stevey-o/bunker/3D_renderings/exterior/01_rear_iso.png

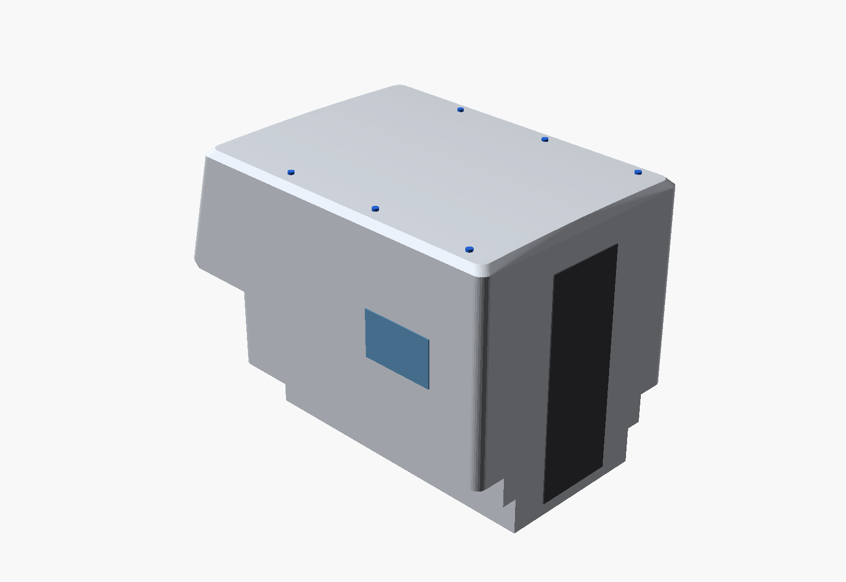
3D_renderings/exterior/01_rear_iso.png
