stevey-o/bunker/3D_renderings/exterior/05_front.png

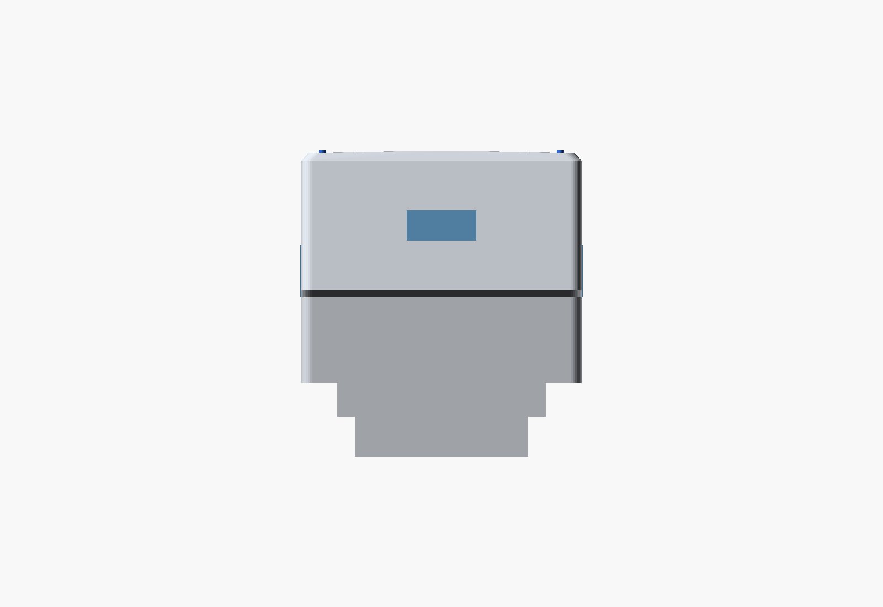
3D_renderings/exterior/05_front.png
