stevey-o/bunker/3D_renderings/exterior/07_top.png

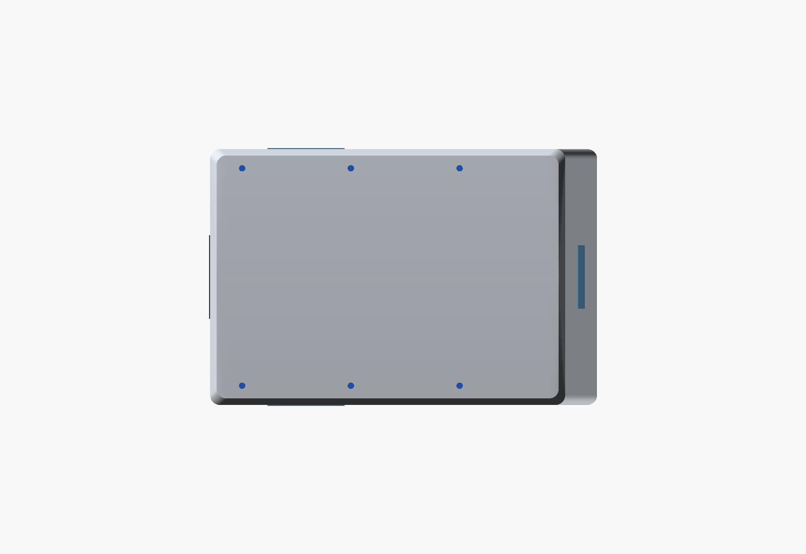
3D_renderings/exterior/07_top.png
