stevey-o/bunker/3D_renderings/fit_study/01_f150_6p5ft.png

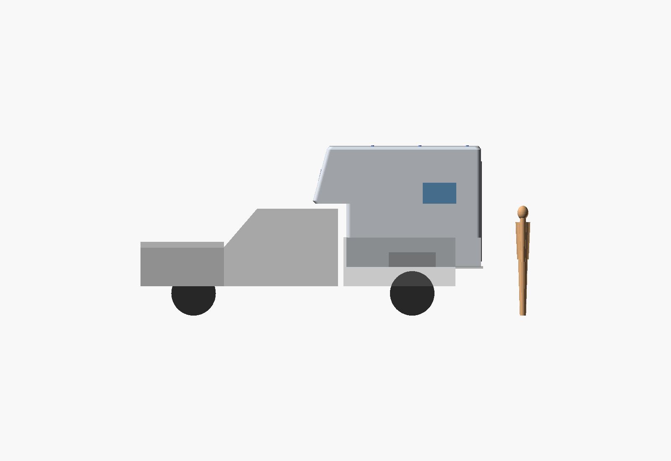
3D_renderings/fit_study/01_f150_6p5ft.png
