stevey-o/bunker/3D_renderings/fit_study/05_tacoma_rear_iso.png

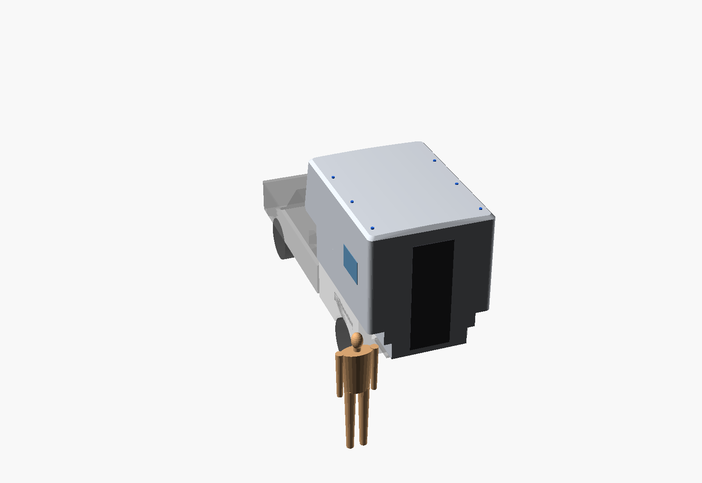
3D_renderings/fit_study/05_tacoma_rear_iso.png
