stevey-o/bunker/3D_renderings/truck_fit/01_short_bed.png

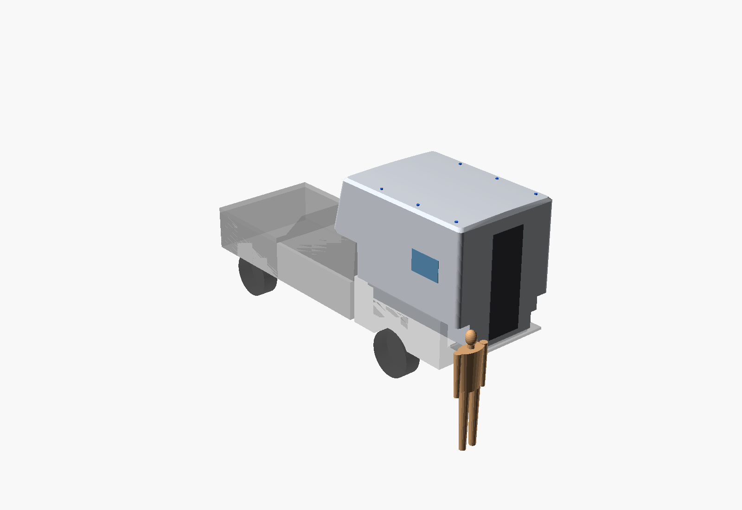
3D_renderings/truck_fit/01_short_bed.png
