stevey-o/bunker/3D_renderings/truck_fit/04_cab_clearance.png

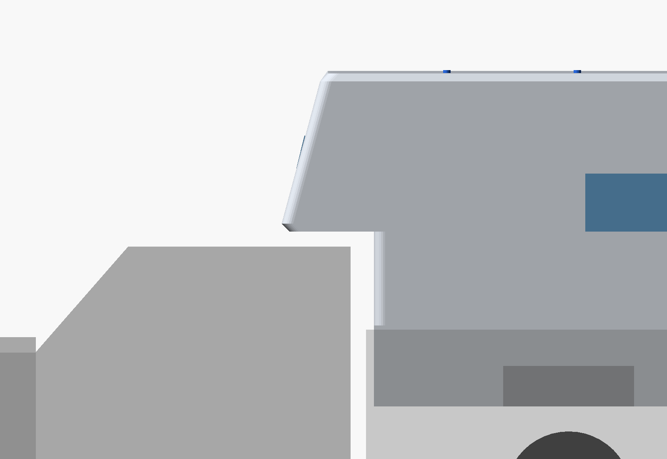
3D_renderings/truck_fit/04_cab_clearance.png
