stevey-o/bunker/cad/config/dimensions.scad

// GENERATED by scripts_code/sync_config.py from cad/config/dimensions.json - DO NOT HAND-EDIT
// Units: inches. Coordinate origin: bed-floor top, centerline, inner face of bed front wall.
// +X forward (toward cab), +Y left (driver), +Z up.

// Build defaults; override with -D (see build_variant.scad).
FRAME_SYSTEM = "HYBRID";
TRUCK = "F350_LONG";
TRUCK_NAMES = ["F350_LONG", "F350_SHORT", "F150_65", "F150_55", "TACOMA_6", "TACOMA_5"];
TRUCK_IDX = search([TRUCK], TRUCK_NAMES)[0];
TAILGATE_DEFAULTS = ["CLOSED", "DOWN", "DOWN", "DOWN", "DOWN", "DOWN"];

WINDOW_NOSE_ENABLED = true;
camper_lower_length = 97.0;
camper_body_width = 80.0;
camper_lower_tub_width = 59.5;
tub_side_clearance = 0.75;
wheel_well_clearance = 1.0;
body_rail_clearance = 1.0;
camper_front_gap = 0.5;
camper_to_cab_clearance = 4.0;
interior_height = 80.0;
floor_sandwich = 3.0;
wall_thickness = 1.75;
roof_thickness = 3.5;
roof_crown = 0.75;
skin_thickness = 0.05;
insulation_thickness = 1.5;
body_corner_radius = 3.0;
roof_edge_radius = 2.0;
nose_projection = 24.0;
nose_top_setback = 10.0;
nose_floor_thickness = 2.5;
door_width = 26.0;
door_height = 72.0;
door_sill_above_floor = 1.0;
door_offset_y = 0.0;
window_side_width = 24.0;
window_side_height = 15.0;
window_side_center_above_floor = 50.0;
window_side_center_from_rear = 30.0;
window_nose_width = 20.0;
window_nose_height = 9.0;
util_profile = "TSLOT_1010";
utility_rail_left_count = 3;
utility_rail_right_count = 3;
utility_rail_front_count = 1;
utility_rail_side_heights = [24.0, 44.0, 64.0];
utility_rail_front_height = 36.0;
utility_rail_end_inset = 2.0;
roof_rack_boss_from_rear = [10.0, 44.0, 78.0];
roof_rack_boss_edge_inset = 6.0;
roof_rack_boss_diameter = 2.0;
roof_rack_boss_height = 0.75;
power_zone_length = 24.0;
power_zone_width = 20.0;
power_zone_from_front = 2.0;
wire_chase_size = 3.0;
human_height = 79.0;
tailgate_clearance = 0.5;
owner_gear_allowance_lb = 300;
truck_bed_floor_height = [39.5, 39.5, 35.0, 35.0, 33.0, 33.0][TRUCK_IDX];
truck_bed_rail_height = [20.0, 20.0, 21.4, 21.4, 19.1, 19.1][TRUCK_IDX];
truck_bed_floor_width = [66.0, 66.0, 65.2, 65.2, 56.7, 56.7][TRUCK_IDX];
truck_bed_inner_width_top = [66.0, 66.0, 65.2, 65.2, 56.7, 56.7][TRUCK_IDX];
truck_bed_rail_width = [6.5, 6.5, 6.5, 6.5, 8.8, 8.8][TRUCK_IDX];
truck_tailgate_opening_width = [61.0, 61.0, 60.0, 60.0, 53.0, 53.0][TRUCK_IDX];
truck_tailgate_length = 20.0;
truck_tailgate_down_offset = 0.5;
truck_wheel_well_width = [50.9, 50.9, 50.6, 50.6, 41.5, 41.5][TRUCK_IDX];
truck_wheel_well_height = 10.5;
truck_wheel_well_length = 34.0;
truck_cab_height_above_bed = [41.5, 41.5, 42.0, 42.0, 37.5, 37.5][TRUCK_IDX];
truck_cab_to_bed_clearance = 4.0;
truck_bed_front_wall_thickness = 1.5;
truck_cab_width = [79.9, 79.9, 79.9, 79.9, 74.4, 74.4][TRUCK_IDX];
truck_cab_roof_length = 58.0;
truck_hood_height_above_bed = [18.0, 18.0, 18.0, 18.0, 12.0, 12.0][TRUCK_IDX];
truck_tire_diameter = [33.0, 33.0, 32.0, 32.0, 31.0, 31.0][TRUCK_IDX];
truck_track_width = [68.0, 68.0, 68.0, 68.0, 63.0, 63.0][TRUCK_IDX];
truck_windshield_run = 24.0;
truck_front_overhang = 38.0;
truck_body_bottom_below_bed = [14.0, 14.0, 14.0, 14.0, 12.0, 12.0][TRUCK_IDX];
truck_beltline_above_bed = [14.0, 14.0, 14.0, 14.0, 10.0, 10.0][TRUCK_IDX];
truck_bed_length = [98.0, 81.8, 78.9, 67.1, 73.7, 60.5][TRUCK_IDX];
truck_rear_axle_from_bulkhead = [51.2, 35.0, 47.9, 36.1, 46.2, 33.0][TRUCK_IDX];
truck_wheelbase = [172.4, 156.2, 157.2, 145.4, 140.6, 127.4][TRUCK_IDX];
tub_base_width = 49.4;
tub_step_z = 11.5;
camper_lower_tub_height = 21.0;
camper_front_x = -0.5;
camper_rear_x = -97.5;
interior_floor_z = 3.0;
ceiling_z = 83.0;
roof_eave_z = 86.5;
roof_crown_z = 87.25;
nose_bottom_z = 45.5;
nose_floor_z = 48.0;
nose_interior_height = 35.0;
nose_front_x = 23.5;
overall_length = 121.0;
overall_height = 87.25;
body_interior_width = 76.5;
tub_interior_base_width = 45.9;
interior_length = 93.5;
door_bottom_z = 4.0;
door_top_z = 76.0;
window_side_center_z = 53.0;
headroom_6ft7 = 1.0;
ground_to_eave = [126.0, 126.0, 121.5, 121.5, 119.5, 119.5][TRUCK_IDX];
ground_to_crown = [126.75, 126.75, 122.25, 122.25, 120.25, 120.25][TRUCK_IDX];
cab_back_x = 5.5;
nose_over_cab = 18.0;
tailgate_x = [-98.0, -81.8, -78.9, -67.1, -73.7, -60.5][TRUCK_IDX];
rear_overhang = [-0.5, 15.7, 18.6, 30.4, 23.8, 37.0][TRUCK_IDX];
rear_axle_x = [-51.2, -35.0, -47.9, -36.1, -46.2, -33.0][TRUCK_IDX];
floor_mid_ahead_of_axle = [2.2, -14.0, -1.1, -12.9, -2.8, -16.0][TRUCK_IDX];
cab_clearance = [4.0, 4.0, 3.5, 3.5, 8.0, 8.0][TRUCK_IDX];
rail_clearance = [1.0, 1.0, -0.4, -0.4, 1.9, 1.9][TRUCK_IDX];
wheel_well_side_clearance = [0.75, 0.75, 0.6, 0.6, -3.95, -3.95][TRUCK_IDX];
wheel_well_top_clearance = 1.0;
tailgate_side_clearance = [0.75, 0.75, 0.25, 0.25, -3.25, -3.25][TRUCK_IDX];
bed_side_clearance = [3.25, 3.25, 2.85, 2.85, -1.4, -1.4][TRUCK_IDX];

// Materials: [name, density_lb_in3]
MATERIALS = [["AL6061T6", 0.0975], ["AL5052H32", 0.0968], ["AL6105T5", 0.0975], ["XPS", 0.0012]];

// Profiles: [name, kind, w, h, wall, material, lb_per_in]
PROFILES = [["TUBE_1X1_083", "SQUARE_TUBE", 1.0, 1.0, 0.083, "AL6061T6", 0.0291], ["TUBE_1X1_125", "SQUARE_TUBE", 1.0, 1.0, 0.125, "AL6061T6", 0.0426], ["TUBE_1X2_125", "RECT_TUBE", 1.0, 2.0, 0.125, "AL6061T6", 0.067], ["TUBE_2X2_125", "SQUARE_TUBE", 2.0, 2.0, 0.125, "AL6061T6", 0.0914], ["TSLOT_1010", "TSLOT", 1.0, 1.0, 0.0, "AL6105T5", 0.0425], ["TSLOT_1020", "TSLOT", 1.0, 2.0, 0.0, "AL6105T5", 0.0763], ["TSLOT_1515", "TSLOT", 1.5, 1.5, 0.0, "AL6105T5", 0.0848]];

// Owner accessory T-slot rails: [id, length, [x,y,z] start, axis]
UTIL_RAILS = [["UTIL-L-01", 89.5, [-93.75, 38.25, 27.0], "X"], ["UTIL-L-02", 89.5, [-93.75, 38.25, 47.0], "X"], ["UTIL-L-03", 89.5, [-93.75, 38.25, 67.0], "X"], ["UTIL-R-01", 89.5, [-93.75, -38.25, 27.0], "X"], ["UTIL-R-02", 89.5, [-93.75, -38.25, 47.0], "X"], ["UTIL-R-03", 89.5, [-93.75, -38.25, 67.0], "X"], ["UTIL-F-01", 72.5, [-2.25, -36.25, 39.0], "Y"]];
